tarantoj/swept-crkbd/gallery/IMG_7885.JPG

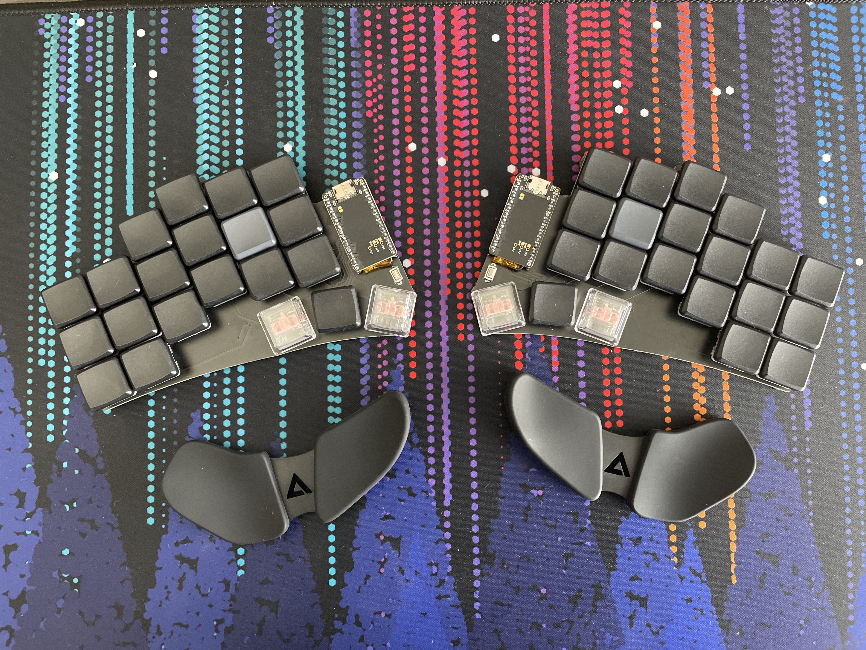
gallery/IMG_7885.JPG
